robotakia-os/ellak2022/3D printing/Εικόνες/arm1.png

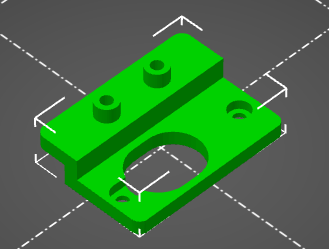
3D printing/Εικόνες/arm1.png
