robotakia-os/ellak2022/3D printing/Εικόνες/arm2.png

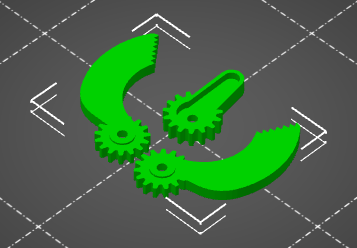
3D printing/Εικόνες/arm2.png
