robotakia-os/ellak2022/3D printing/Εικόνες/arm3.png

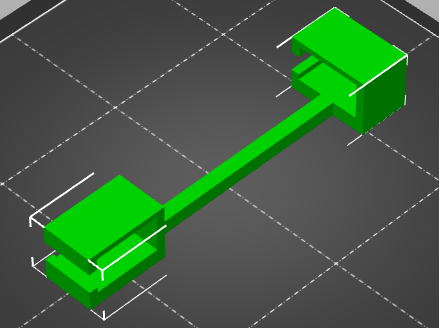
3D printing/Εικόνες/arm3.png
