robotakia-os/ellak2022/3D printing/Εικόνες/cog.png

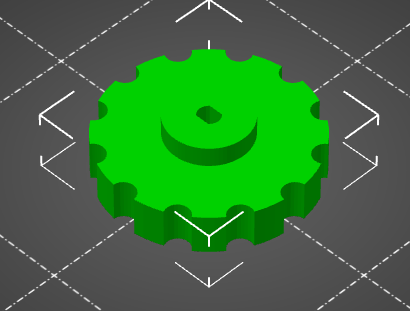
3D printing/Εικόνες/cog.png
