robotakia-os/ellak2022/3D printing/Εικόνες/cog_bracket_outer.png

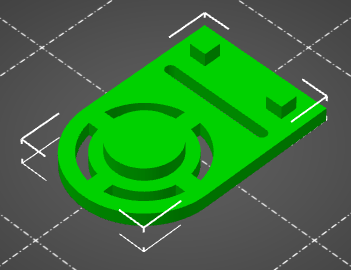
3D printing/Εικόνες/cog_bracket_outer.png
