robotakia-os/ellak2022/3D printing/Εικόνες/track.png

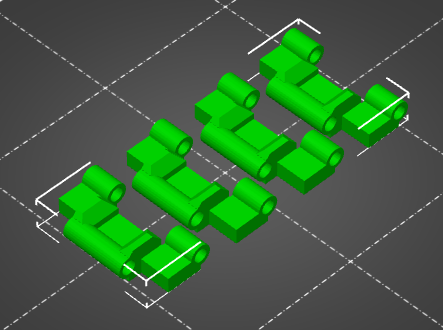
3D printing/Εικόνες/track.png
