robotakia-os/ellak2022/3D printing/Εικόνες/wheel_pin.png

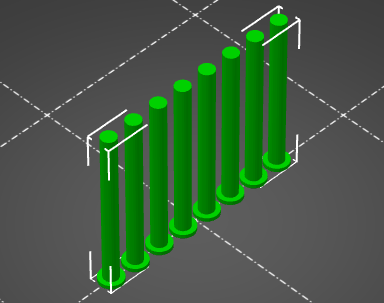
3D printing/Εικόνες/wheel_pin.png
